dennowiggle/FLEADiP/kicad/FLEADiP.kicad_sch

## KiCad design kicad/FLEADiP.kicad_sch (2023-07-13)

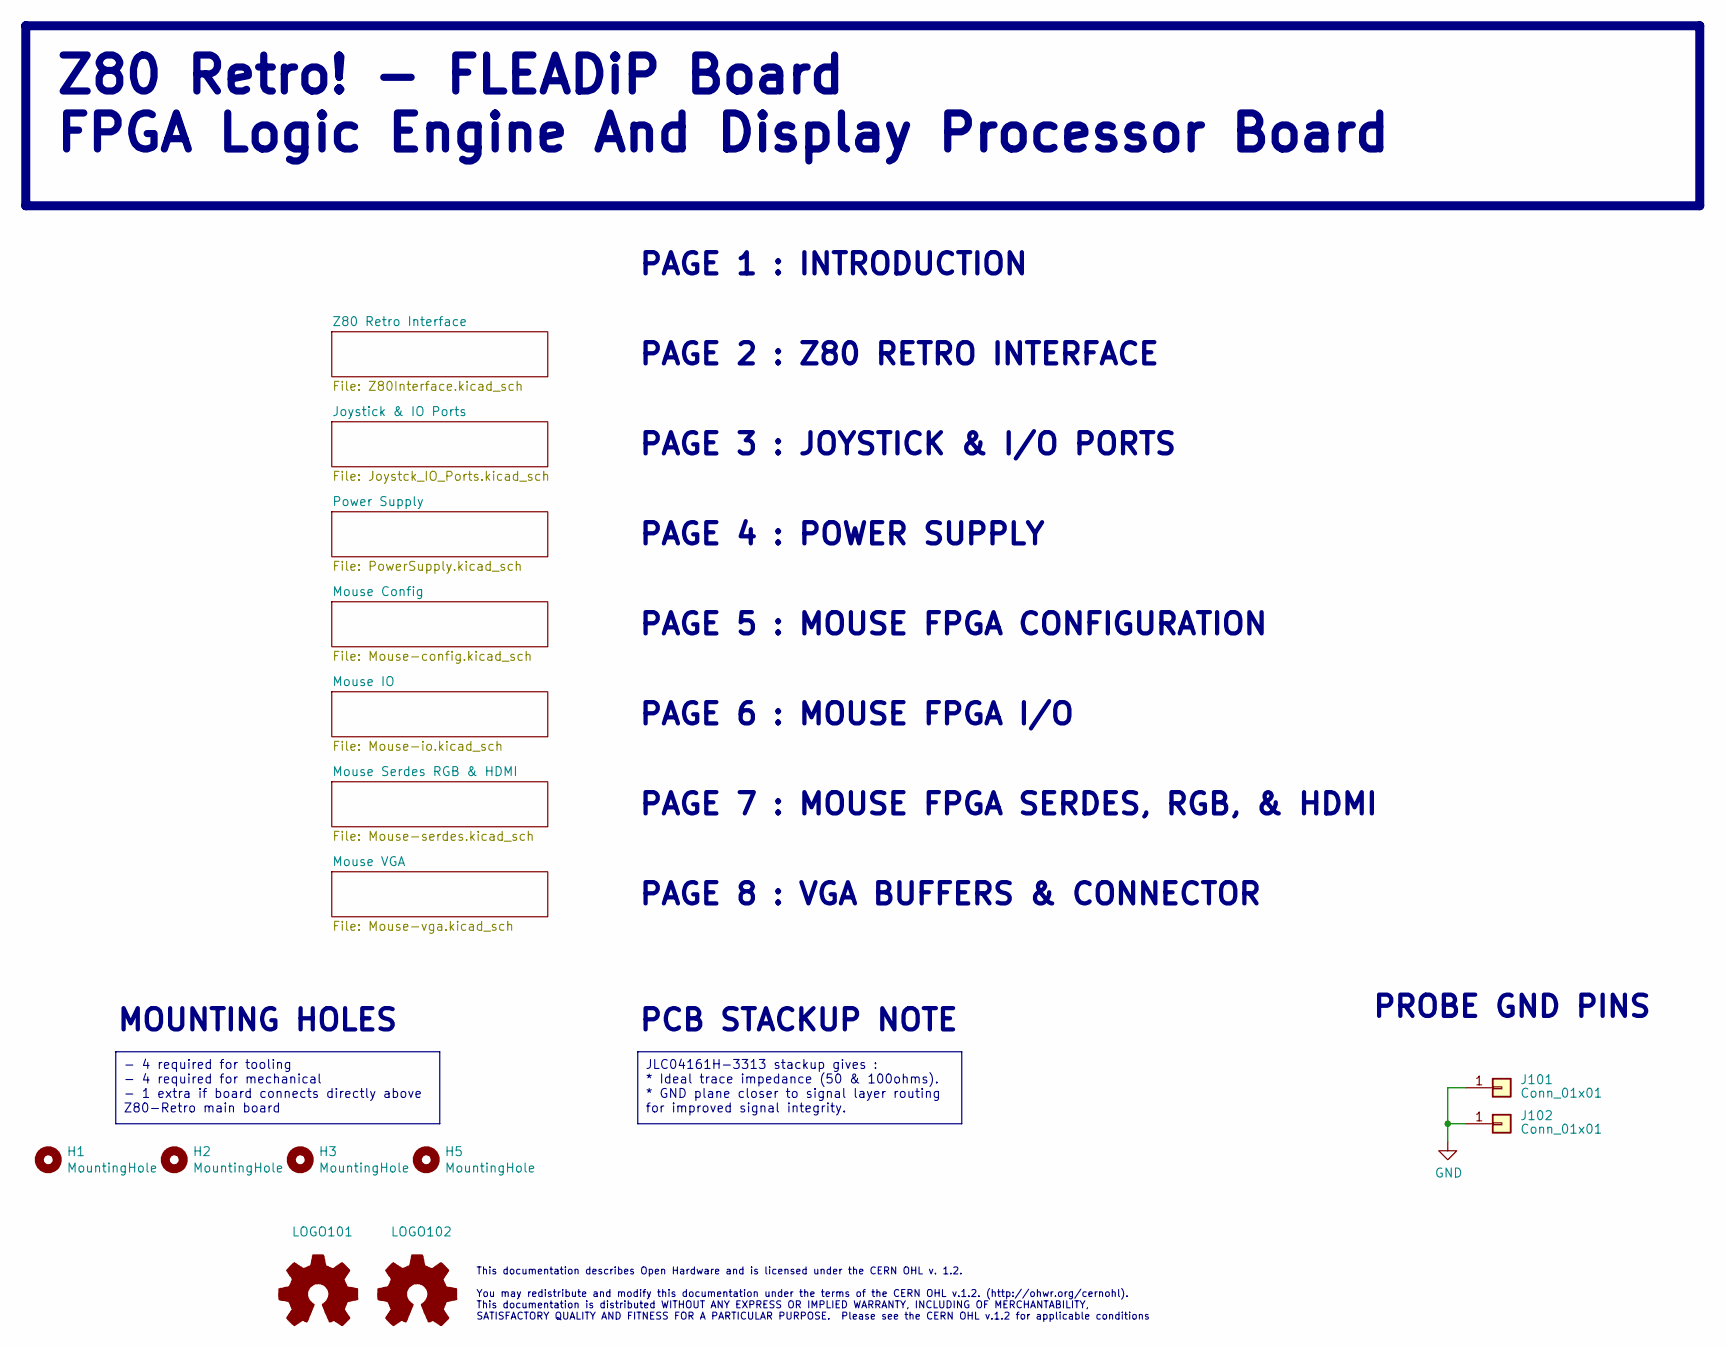
[picture p20: schematic FLEADiP.kicad_sch]

Parts:
H1, H2, H3, H5: MountingHole; MountingHole_2.7mm_M2.5_DIN965
J101, J102: Conn_01x01; PinHeader_1x01_P2.54mm_Vertical
LOGO101, LOGO102: Logo_Open_Hardware_Small; OSHW-Logo_7.5x8mm_SilkScreen

Connections:
GND: J101.1, J102.1

Notes on the sheet:
Z80 Retro! - FLEADiP Board FPGA Logic Engine And Display Processor Board
JLC04161H-3313 stackup gives : * Ideal trace impedance (50 & 100ohms). * GND plane closer to signal layer routing for improved signal integrity.
- 4 required for tooling - 4 required for mechanical - 1 extra if board connects directly above Z80-Retro main board
MOUNTING HOLES
PAGE 5 : MOUSE FPGA CONFIGURATION
PAGE 6 : MOUSE FPGA I/O
PAGE 4 : POWER SUPPLY
PAGE 2 : Z80 RETRO INTERFACE
PCB STACKUP NOTE
PAGE 7 : MOUSE FPGA SERDES, RGB, & HDMI
PROBE GND PINS
PAGE 8 : VGA BUFFERS & CONNECTOR
PAGE 1 : INTRODUCTION
PAGE 3 : JOYSTICK & I/O PORTS
This documentation describes Open Hardware and is licensed under the CERN OHL v. 1.2. You may redistribute and modify this documentation under the terms of the CERN OHL v.1.2. (http://ohwr.org/cernohl). This documentation is distributed WITHOUT ANY EXPRESS OR IMPLIED WARRANTY, INCLUDING OF MERCHANT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
