dennowiggle/FLEADiP/kicad/Joystck_IO_Ports.kicad_sch

## KiCad design kicad/Joystck_IO_Ports.kicad_sch (2023-07-13)

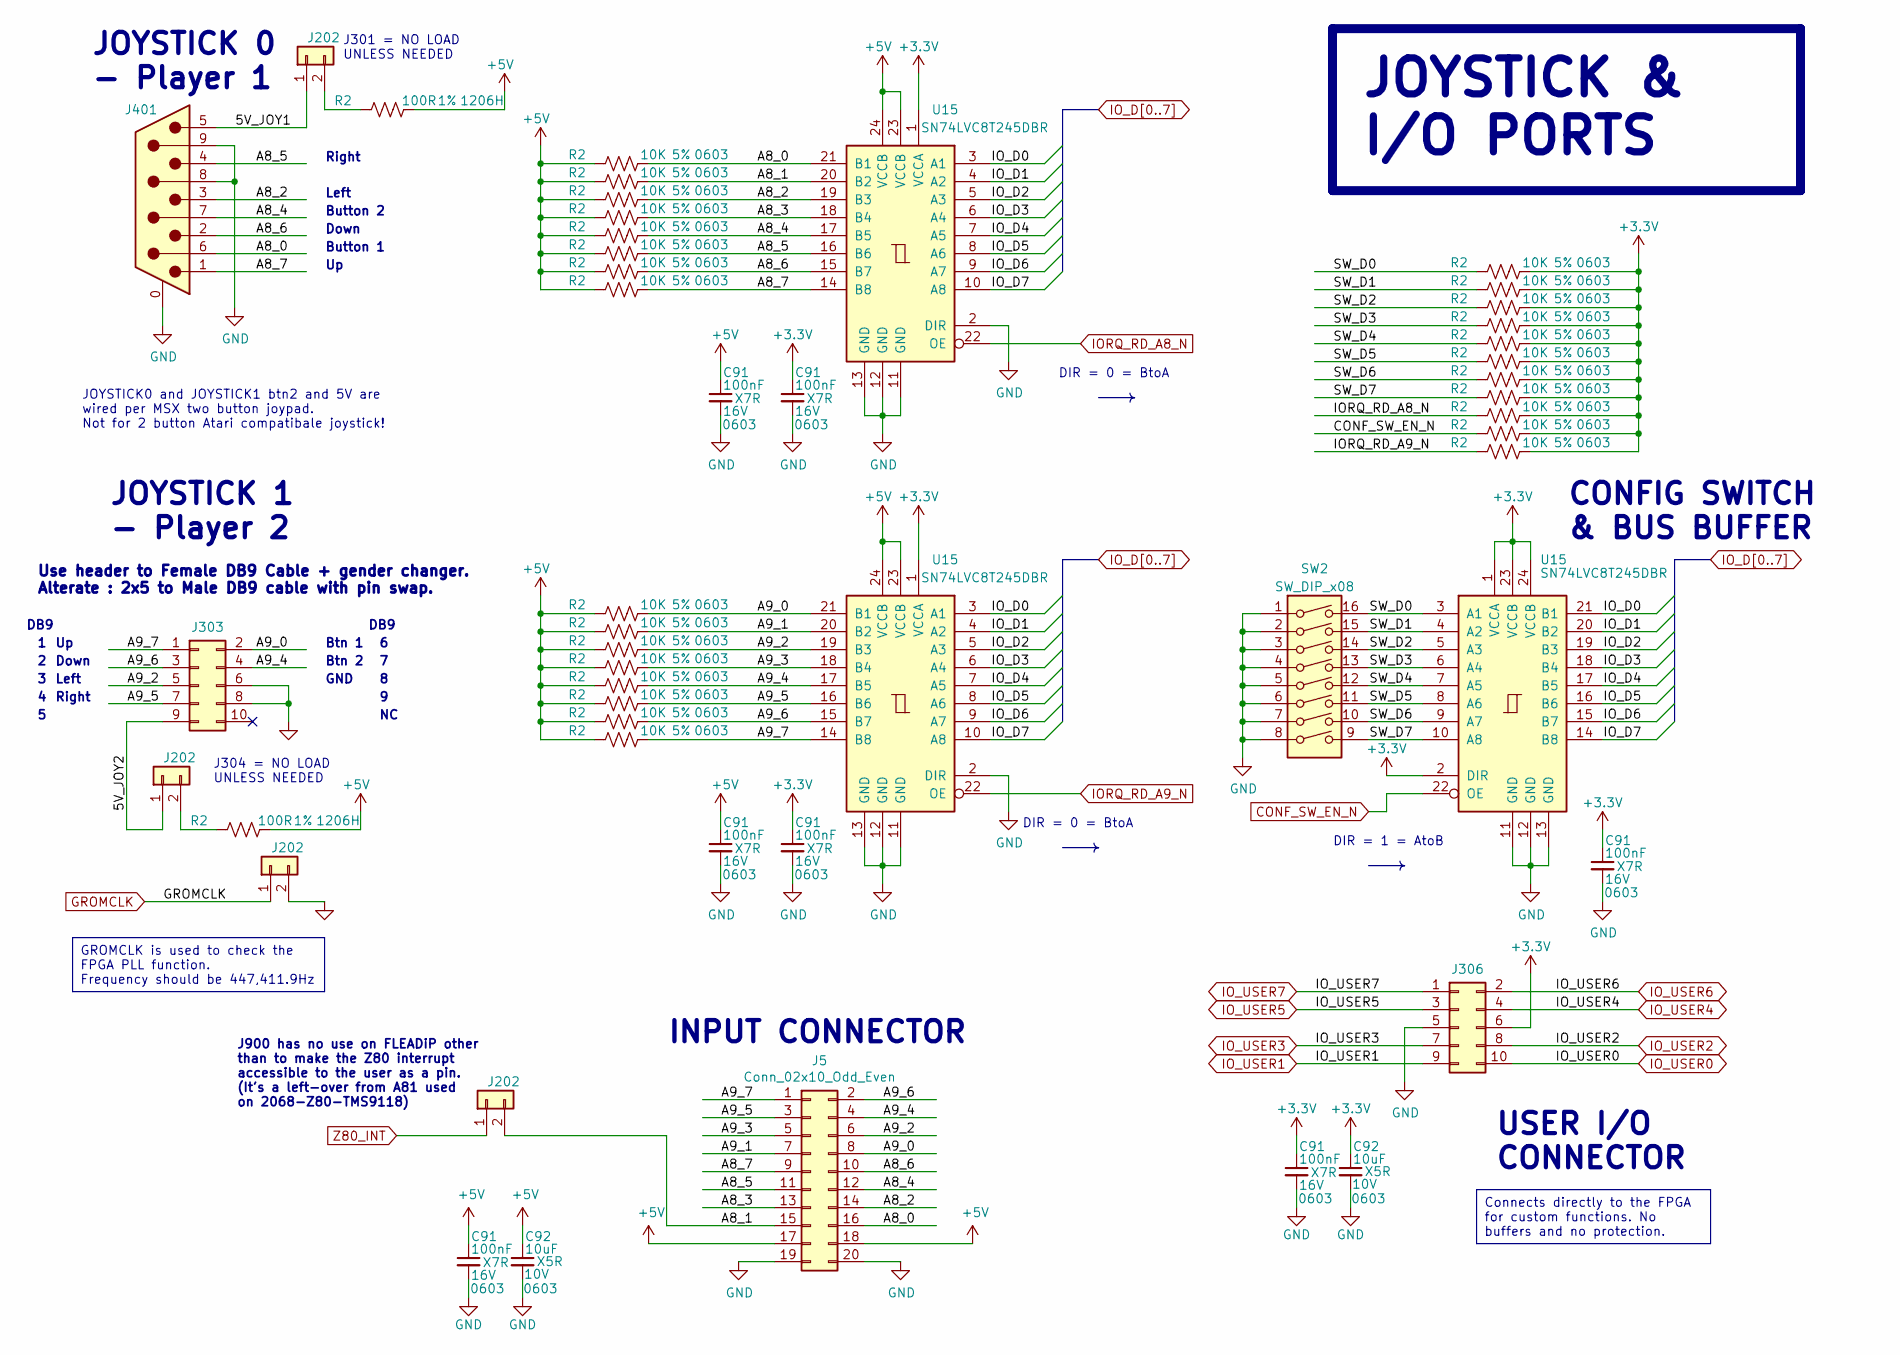
[picture p21: schematic Joystck_IO_Ports.kicad_sch]

Parts:
C91: 100nF; C_0603_1608Metric; Voltage 16V; Tolerance 10%; MPN CC0603KRX7R7BB104; Digikey 311-1088-1-ND
C92: 10uF; C_0603_1608Metric; Voltage 10V; Tolerance 10%; MPN CC0603KRX5R6BB106; Digikey 311-1782-1-ND
J5: Conn_02x10_Odd_Even; PinHeader_2x10_P2.54mm_Vertical; MPN PH2-20-UA; Digi-Key_PN 2057-PH2-20-UA-ND
J202: Conn_01x02; PinHeader_1x02_P2.54mm_Vertical; MPN PH1-02-UA; Digi-Key_PN 2057-PH1-02-UA-ND
J303, J306: Conn_02x05; PinHeader_2x05_P2.54mm_Vertical; MPN PR20205VBDN; Digikey 1849-1002-ND
J401: DB9_Male_MountingHoles; DSUB-9_Male_Horizontal_P2.77x2.84mm_EdgePinOffset7.70mm_Hou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; MPN A-DS 09 A/KG-T4S; Digikey AE10970-ND
R2: 10K; R_0603_1608Metric; Tolerance 5%; MPN RC0603JR-0710KL; Digikey 311-10KGRCT-ND
SW2: SW_DIP_x08; SW_DIP_SPSTx08_Slide_9.78x22.5mm_W7.62mm_P2.54mm; MPN 206-8ST; Digikey CT2068ST-ND
U15: SN74LVC8T245DBR; SSOP-24_5.3x8.2mm_P0.65mm; MPN SN74LVC8T245DBR; Digikey 296-21065-1-ND

Connections:
5V_JOY1: J202.1, J401.5
5V_JOY2: J202.1, J303.9
+3.3V: C91.1, C92.1, J306.6, R2.2, U15.1 (VCCA), U15.2 (DIR), U15.23 (VCCB), U15.24 (VCCB)
+5V: C91.1, C92.1, J5.17, J5.18, R2.1, R2.2, U15.23 (VCCB), U15.24 (VCCB)
A8_0: J5.16, J401.6, R2.2, U15.21 (B1)
A8_1: J5.15, J202.2, R2.2, U15.20 (B2)
A8_2: J5.14, J401.3, R2.2, U15.19 (B3)
A8_3: J5.13, R2.2, U15.18 (B4)
A8_4: J5.12, J401.7, R2.2, U15.17 (B5)
A8_5: J5.11, J401.4, R2.2, U15.16 (B6)
A8_6: J5.10, J401.2, R2.2, U15.15 (B7)
A8_7: J5.9, J401.1, R2.2, U15.14 (B8)
A9_0: J5.8, J303.2, R2.2, U15.21 (B1)
A9_1: J5.7, R2.2, U15.20 (B2)
A9_2: J5.6, J303.5, R2.2, U15.19 (B3)
A9_3: J5.5, R2.2, U15.18 (B4)
A9_4: J5.4, J303.4, R2.2, U15.17 (B5)
A9_5: J5.3, J303.7, R2.2, U15.16 (B6)
A9_6: J5.2, J303.3, R2.2, U15.15 (B7)
A9_7: J5.1, J303.1, R2.2, U15.14 (B8)
CONF_SW_EN_N: R2.1, U15.22 (OE)
GND: C91.2, C92.2, J5.19, J5.20, J202.2, J303.6, J303.8, J306.5, J401.0 (PAD), J401.8, J401.9, SW2.1, SW2.2, SW2.3, SW2.4, SW2.5, SW2.6, SW2.7, SW2.8, U15.2 (DIR), U15.11 (GND), U15.12 (GND), U15.13 (GND)
GROMCLK: J202.1
IORQ_RD_A8_N: R2.1, U15.22 (OE)
IORQ_RD_A9_N: R2.1, U15.22 (OE)
IO_D0: U15.3 (A1), U15.21 (B1)
IO_D1: U15.4 (A2), U15.20 (B2)
IO_D2: U15.5 (A3), U15.19 (B3)
IO_D3: U15.6 (A4), U15.18 (B4)
IO_D4: U15.7 (A5), U15.17 (B5)
IO_D5: U15.8 (A6), U15.16 (B6)
IO_D6: U15.9 (A7), U15.15 (B7)
IO_D7: U15.10 (A8), U15.14 (B8)
IO_USER0: J306.10
IO_USER1: J306.9
IO_USER2: J306.8
IO_USER3: J306.7
IO_USER4: J306.4
IO_USER5: J306.3
IO_USER6: J306.2
IO_USER7: J306.1
unnamed: J202.2, R2.1
SW_D0: R2.1, SW2.16, U15.3 (A1)
SW_D1: R2.1, SW2.15, U15.4 (A2)
SW_D2: R2.1, SW2.14, U15.5 (A3)
SW_D3: R2.1, SW2.13, U15.6 (A4)
SW_D4: R2.1, SW2.12, U15.7 (A5)
SW_D5: R2.1, SW2.11, U15.8 (A6)
SW_D6: R2.1, SW2.10, U15.9 (A7)
SW_D7: R2.1, SW2.9, U15.10 (A8)
Z80_INT: J202.1

Notes on the sheet:
GROMCLK is used to check the FPGA PLL function. Frequency should be 447,411.9Hz
Connects directly to the FPGA for custom functions. No buffers and no protection.
JOYSTICK & I/O PORTS
Button 1
GND
DB9
J900 has no use on FLEADiP other than to make the Z80 interrupt accessible to the user as a pin. (It's a left-over from A81 used on 2068-Z80-TMS9118)
Left
Down
J301 = NO LOAD UNLESS NEEDED
INPUT CONNECTOR
J304 = NO LOAD UNLESS NEEDED
DIR = 0 = BtoA
USER I/O CONNECTOR
CONFIG SWITCH & BUS BUFFER
Use header to Female DB9 Cable + gender changer. Alterate : 2x5 to Male DB9 cable with pin swap.
Right
Btn 2
Btn 1
JOYSTICK 1 - Player 2
JOYSTICK0 and JOYSTICK1 btn2 and 5V are wired per MSX two button joypad. Not for 2 button Atari compatibale joystick!
Button 2
JOYSTICK 0 - Player 1
DIR = 1 = AtoB
