dennowiggle/FLEADiP/kicad/Mouse-config.kicad_sch

## KiCad design kicad/Mouse-config.kicad_sch (2023-07-13)

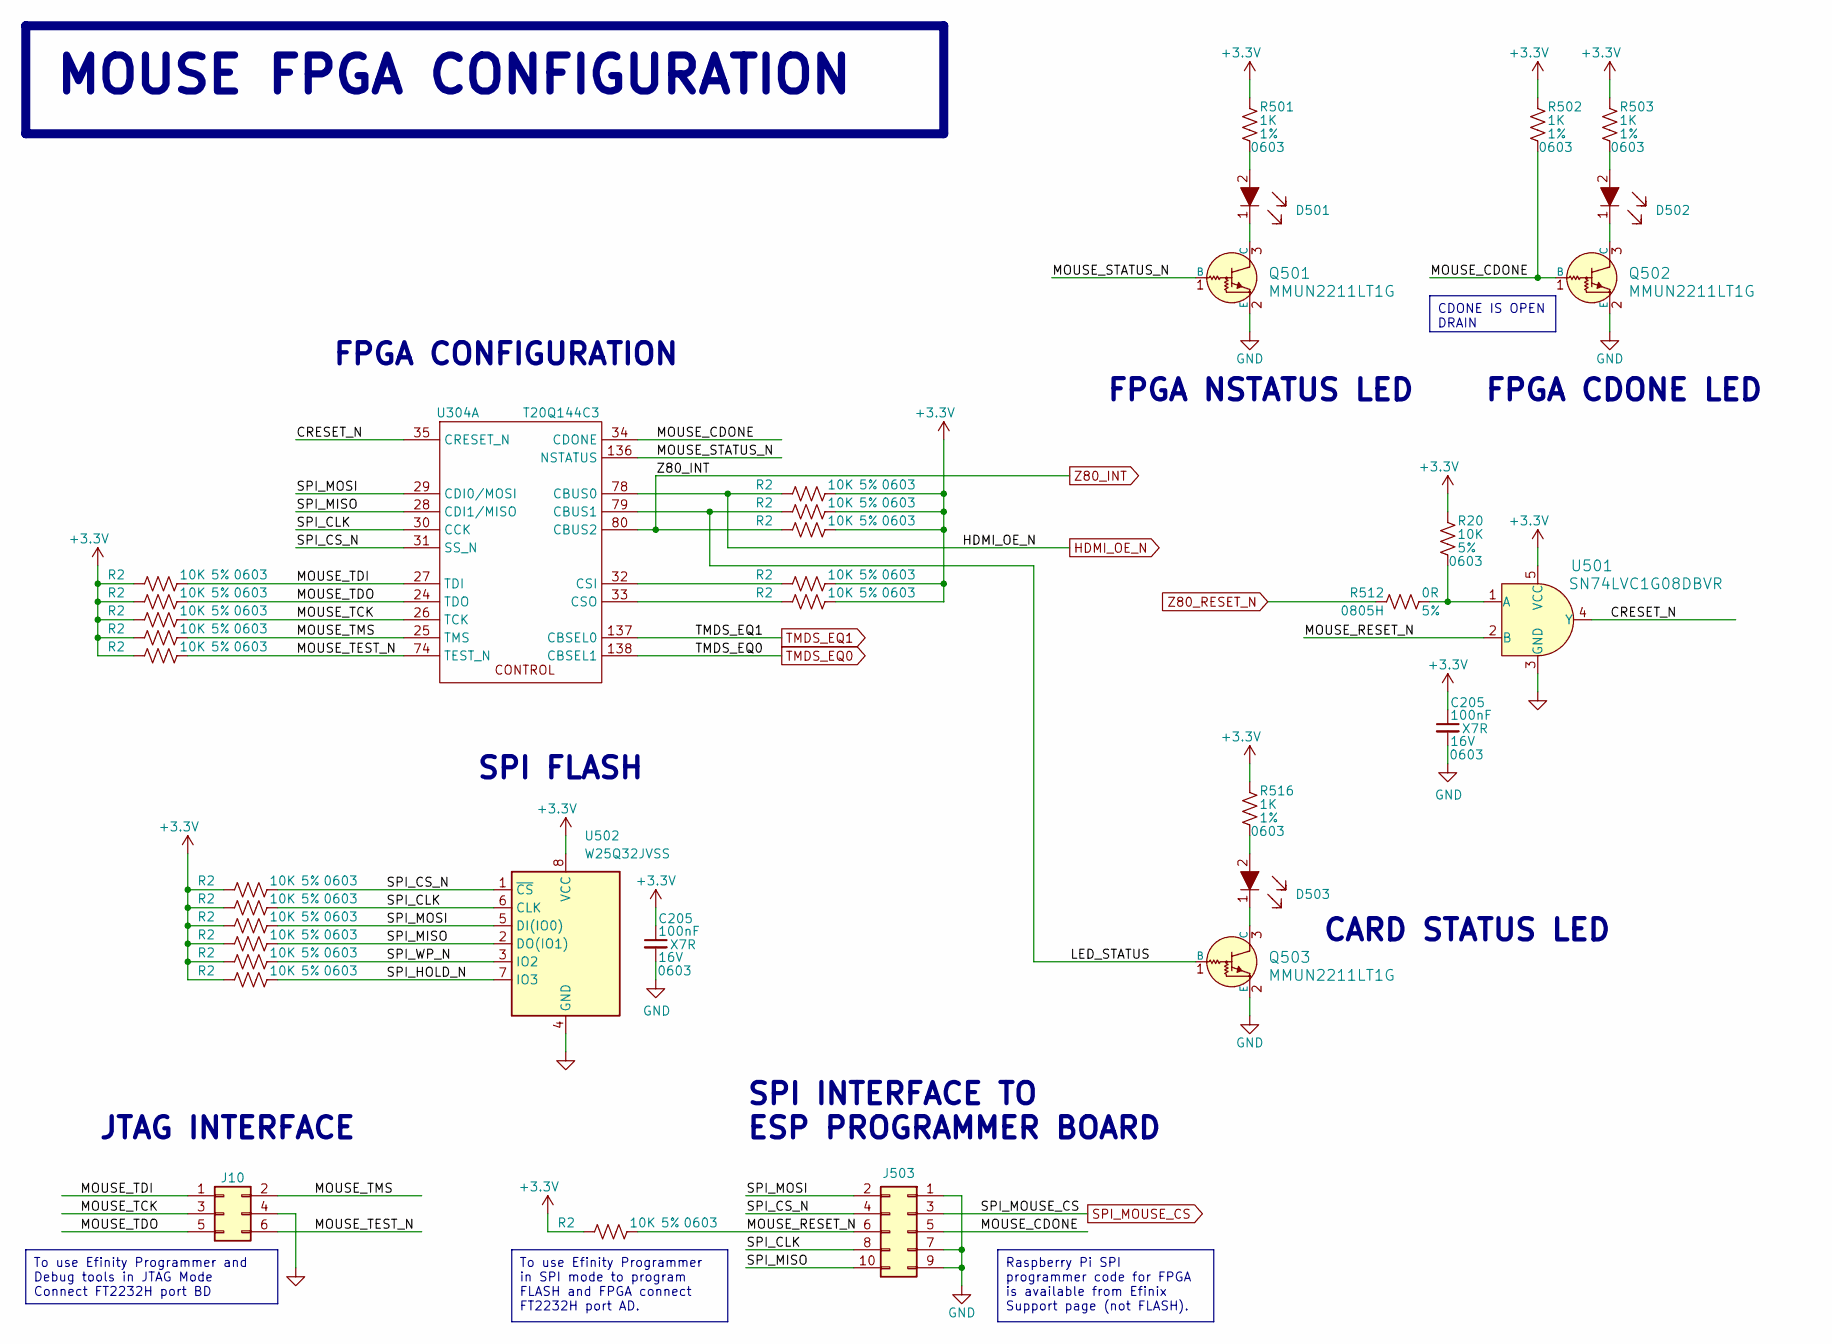
[picture p22: schematic Mouse-config.kicad_sch]

Parts:
C205: 100nF; C_0603_1608Metric; Voltage 16V; Tolerance 10%; MPN CC0603KRX7R7BB104; Digikey 311-1088-1-ND
D501, D502, D503: LTST-C191KRKT; LED_0603_1608Metric; MPN LTST-C191GKT; Digikey 160-1443-1-ND
J10: Conn_02x03; PinHeader_2x03_P2.54mm_Vertical; MPN PH2-06-UA; Digikey 2057-PH2-06-UA-ND
J503: Conn_02x05_Right_Angle; PinSocket_2x05_P2.54mm_Vertical; MPN PH2RA-10-UA; Digikey 2057-PH2RA-10-UA-ND
Q501, Q502, Q503: MMUN2211LT1G; SOT-23-3; MPN MMUN2211LT1G; Digikey MMUN2211LT1GOSCT-ND
R2, R20: 10K; R_0603_1608Metric; Tolerance 5%; MPN RC0603JR-0710KL; Digikey 311-10KGRCT-ND
R501, R502, R503, R516: 1K; R_0603_1608Metric; Tolerance 1%; MPN RC0603FR-071KL; Digikey 311-1.00KHRCT-ND
R512: 0R; R_0805_2012Metric_Pad1.20x1.40mm_HandSolder; Tolerance 5%; MPN RC0805JR-070RL; Digikey 311-0.0ARCT-ND
U304: T20Q144C3; LQFP-144_20x20mm_P0.5mm; MPN T20Q144C3; Digikey 2134-T20Q144C3-ND
U501: SN74LVC1G08DBVR; SOT-23-5; MPN SN74LVC1G08DBVR; Digikey 296-11601-1-ND
U502: W25Q32JVSS; SOIC-8_5.23x5.23mm_P1.27mm; MPN W25Q32JVSSIQ; Digikey W25Q32JVSSIQCT-ND

Connections:
+3.3V: C205.1, R2.1, R2.2, R20.1, R501.1, R502.1, R503.1, R516.1, U501.5 (VCC), U502.8 (VCC)
CRESET_N: U304.35 (CRESET_N), U501.4 (Y)
GND: C205.2, J10.4, J503.1, J503.7, J503.9, Q501.2 (E), Q502.2 (E), Q503.2 (E), U501.3 (GND), U502.4 (GND)
HDMI_OE_N: R2.1, U304.78 (CBUS0)
LED_STATUS: Q503.1 (B), R2.1, U304.79 (CBUS1)
MOUSE_CDONE: J503.5, Q502.1 (B), R502.2, U304.34 (CDONE)
MOUSE_RESET_N: J503.6, R2.2, U501.2 (B)
MOUSE_STATUS_N: Q501.1 (B), U304.136 (NSTATUS)
MOUSE_TCK: J10.3, R2.2, U304.26 (TCK)
MOUSE_TDI: J10.1, R2.2, U304.27 (TDI)
MOUSE_TDO: J10.5, R2.2, U304.24 (TDO)
MOUSE_TEST_N: J10.6, R2.2, U304.74 (TEST_N)
MOUSE_TMS: J10.2, R2.2, U304.25 (TMS)
unnamed: D501.1, Q501.3 (C)
unnamed: D501.2, R501.2
unnamed: D502.1, Q502.3 (C)
unnamed: D502.2, R503.2
unnamed: D503.1, Q503.3 (C)
unnamed: D503.2, R516.2
unnamed: R2.1, U304.32 (CSI), U304.33 (CSO)
unnamed: R20.2, R512.2, U501.1 (A)
SPI_CLK: J503.8, R2.2, U304.30 (CCK), U502.6 (CLK)
SPI_CS_N: J503.4, R2.2, U304.31 (SS_N), U502.1 (~CS)
SPI_HOLD_N: R2.2, U502.7 (IO3)
SPI_MISO: J503.10, R2.2, U304.28 (CDI1/MISO), U502.2 (DO(IO1))
SPI_MOSI: J503.2, R2.2, U304.29 (CDI0/MOSI), U502.5 (DI(IO0))
SPI_MOUSE_CS: J503.3
SPI_WP_N: R2.2, U502.3 (IO2)
TMDS_EQ0: U304.138 (CBSEL1)
TMDS_EQ1: U304.137 (CBSEL0)
Z80_INT: R2.1, U304.80 (CBUS2)
Z80_RESET_N: R512.1

Notes on the sheet:
CDONE IS OPEN DRAIN
To use Efinity Programmer in SPI mode to program FLASH and FPGA connect FT2232H port AD.
Raspberry Pi SPI programmer code for FPGA is available from Efinix Support page (not FLASH).
MOUSE FPGA CONFIGURATION
To use Efinity Programmer and Debug tools in JTAG Mode Connect FT2232H port BD
SPI FLASH
JTAG INTERFACE
CARD STATUS LED
SPI INTERFACE TO ESP PROGRAMMER BOARD
FPGA NSTATUS LED
FPGA CONFIGURATION
FPGA CDONE LED
