dennowiggle/FLEADiP/kicad/Mouse-io.kicad_sch

## KiCad design kicad/Mouse-io.kicad_sch (2023-07-13)

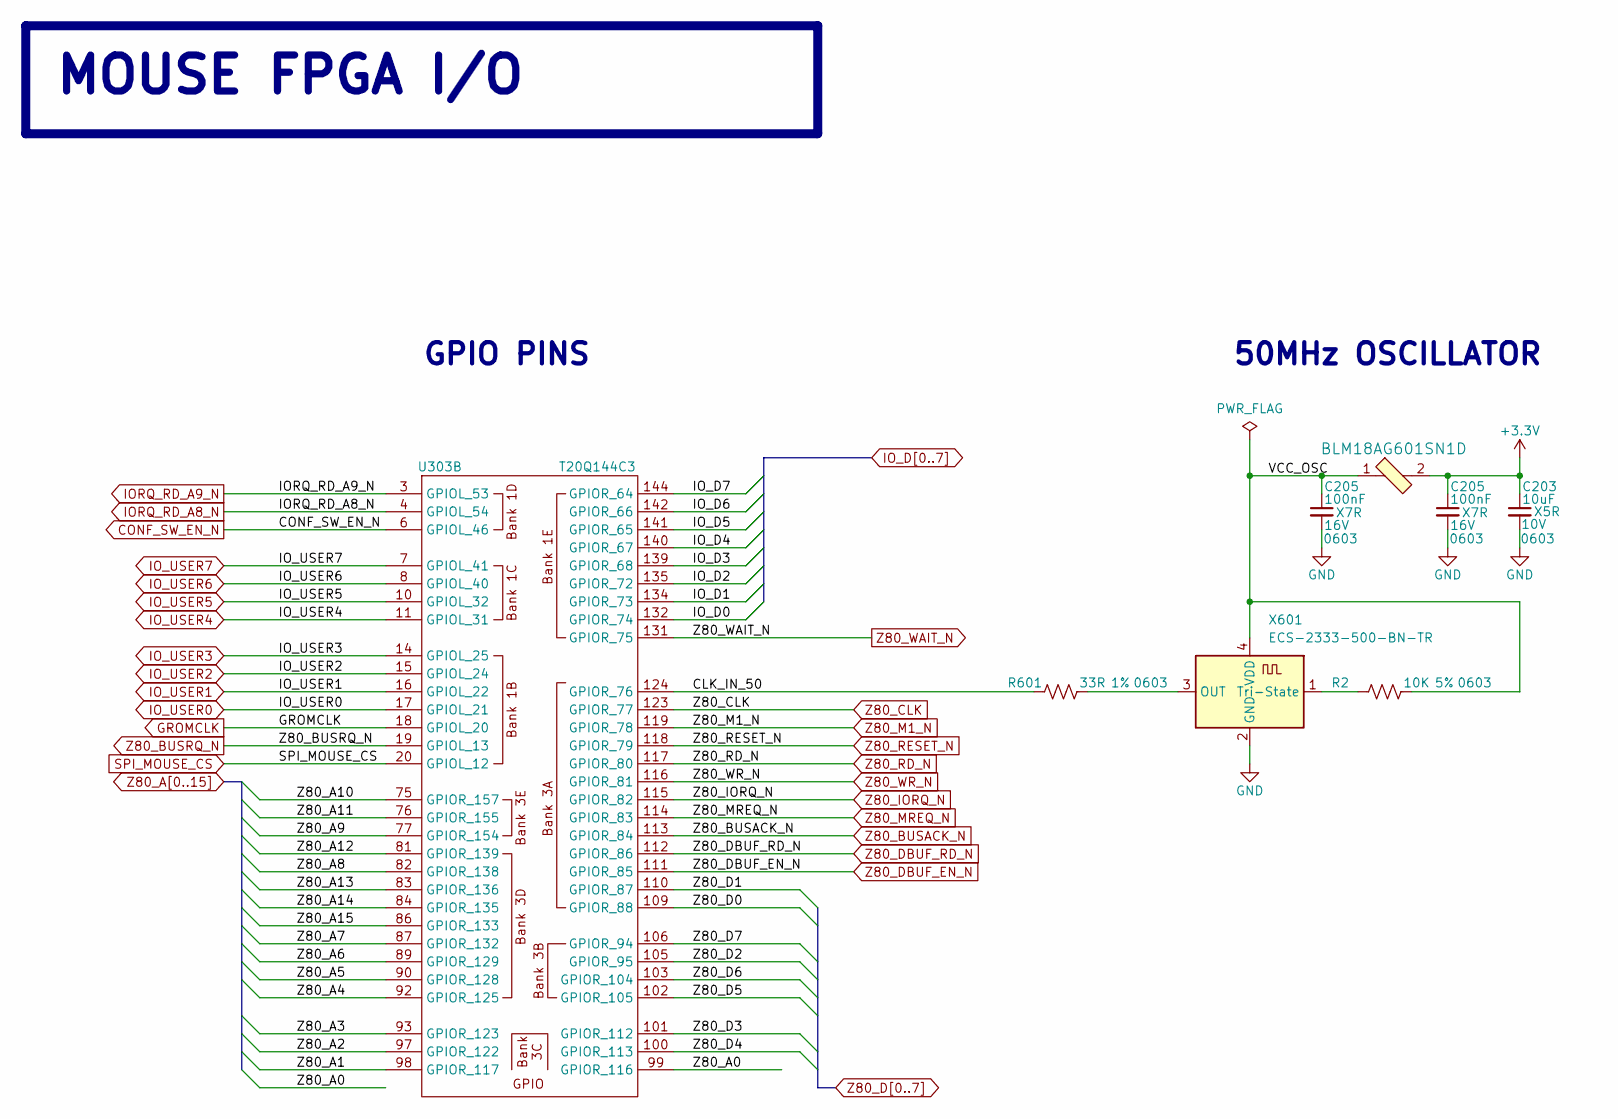
[picture p23: schematic Mouse-io.kicad_sch]

Parts:
C203: 10uF; C_0603_1608Metric; Voltage 10V; Tolerance 10%; MPN CC0603KRX5R6BB106; Digikey 311-1782-1-ND
C205: 100nF; C_0603_1608Metric; Voltage 16V; Tolerance 10%; MPN CC0603KRX7R7BB104; Digikey 311-1088-1-ND
FB2: BLM18AG601SN1D; L_0603_1608Metric; MPN BLM18AG601SN1D; Digikey 490-1014-1-ND
R2: 10K; R_0603_1608Metric; Tolerance 5%; MPN RC0603JR-0710KL; Digikey 311-10KGRCT-ND
R601: 33R; R_0603_1608Metric; Tolerance 1%; MPN RC0603FR-0733RL; Digikey 13-RC0603FR-0733RLCT-ND
U303: T20Q144C3; LQFP-144_20x20mm_P0.5mm; MPN T20Q144C3; Digikey 2134-T20Q144C3-ND
X601: ECS-2333-500-BN-TR; Oscillator_SMD_EuroQuartz_XO32-4Pin_3.2x2.5mm; MPN ECS-2333-500-BN-TR; Digikey XC1930CT-ND

Connections:
+3.3V: C203.1, C205.1, FB2.2
CLK_IN_50: R601.1, U303.124 (GPIOR_76)
CONF_SW_EN_N: U303.6 (GPIOL_46)
GND: C203.2, C205.2, X601.2 (GND)
GROMCLK: U303.18 (GPIOL_20)
IORQ_RD_A8_N: U303.4 (GPIOL_54)
IORQ_RD_A9_N: U303.3 (GPIOL_53)
IO_D0: U303.132 (GPIOR_74)
IO_D1: U303.134 (GPIOR_73)
IO_D2: U303.135 (GPIOR_72)
IO_D3: U303.139 (GPIOR_68)
IO_D4: U303.140 (GPIOR_67)
IO_D5: U303.141 (GPIOR_65)
IO_D6: U303.142 (GPIOR_66)
IO_D7: U303.144 (GPIOR_64)
IO_USER0: U303.17 (GPIOL_21)
IO_USER1: U303.16 (GPIOL_22)
IO_USER2: U303.15 (GPIOL_24)
IO_USER3: U303.14 (GPIOL_25)
IO_USER4: U303.11 (GPIOL_31)
IO_USER5: U303.10 (GPIOL_32)
IO_USER6: U303.8 (GPIOL_40)
IO_USER7: U303.7 (GPIOL_41)
unnamed: R2.1, X601.1 (Tri-State)
unnamed: R601.2, X601.3 (OUT)
SPI_MOUSE_CS: U303.20 (GPIOL_12)
VCC_OSC: C205.1, FB2.1, R2.2, X601.4 (VDD)
Z80_A0: U303.99 (GPIOR_116)
Z80_A1: U303.98 (GPIOR_117)
Z80_A2: U303.97 (GPIOR_122)
Z80_A3: U303.93 (GPIOR_123)
Z80_A4: U303.92 (GPIOR_125)
Z80_A5: U303.90 (GPIOR_128)
Z80_A6: U303.89 (GPIOR_129)
Z80_A7: U303.87 (GPIOR_132)
Z80_A8: U303.82 (GPIOR_138)
Z80_A9: U303.77 (GPIOR_154)
Z80_A10: U303.75 (GPIOR_157)
Z80_A11: U303.76 (GPIOR_155)
Z80_A12: U303.81 (GPIOR_139)
Z80_A13: U303.83 (GPIOR_136)
Z80_A14: U303.84 (GPIOR_135)
Z80_A15: U303.86 (GPIOR_133)
Z80_BUSACK_N: U303.113 (GPIOR_84)
Z80_BUSRQ_N: U303.19 (GPIOL_13)
Z80_CLK: U303.123 (GPIOR_77)
Z80_D0: U303.109 (GPIOR_88)
Z80_D1: U303.110 (GPIOR_87)
Z80_D2: U303.105 (GPIOR_95)
Z80_D3: U303.101 (GPIOR_112)
Z80_D4: U303.100 (GPIOR_113)
Z80_D5: U303.102 (GPIOR_105)
Z80_D6: U303.103 (GPIOR_104)
Z80_D7: U303.106 (GPIOR_94)
Z80_DBUF_EN_N: U303.111 (GPIOR_85)
Z80_DBUF_RD_N: U303.112 (GPIOR_86)
Z80_IORQ_N: U303.115 (GPIOR_82)
Z80_M1_N: U303.119 (GPIOR_78)
Z80_MREQ_N: U303.114 (GPIOR_83)
Z80_RD_N: U303.117 (GPIOR_80)
Z80_RESET_N: U303.118 (GPIOR_79)
Z80_WAIT_N: U303.131 (GPIOR_75)
Z80_WR_N: U303.116 (GPIOR_81)

Notes on the sheet:
MOUSE FPGA I/O
50MHz OSCILLATOR
GPIO PINS
