dennowiggle/FLEADiP/kicad/Mouse-serdes.kicad_sch

## KiCad design kicad/Mouse-serdes.kicad_sch (2023-07-13)

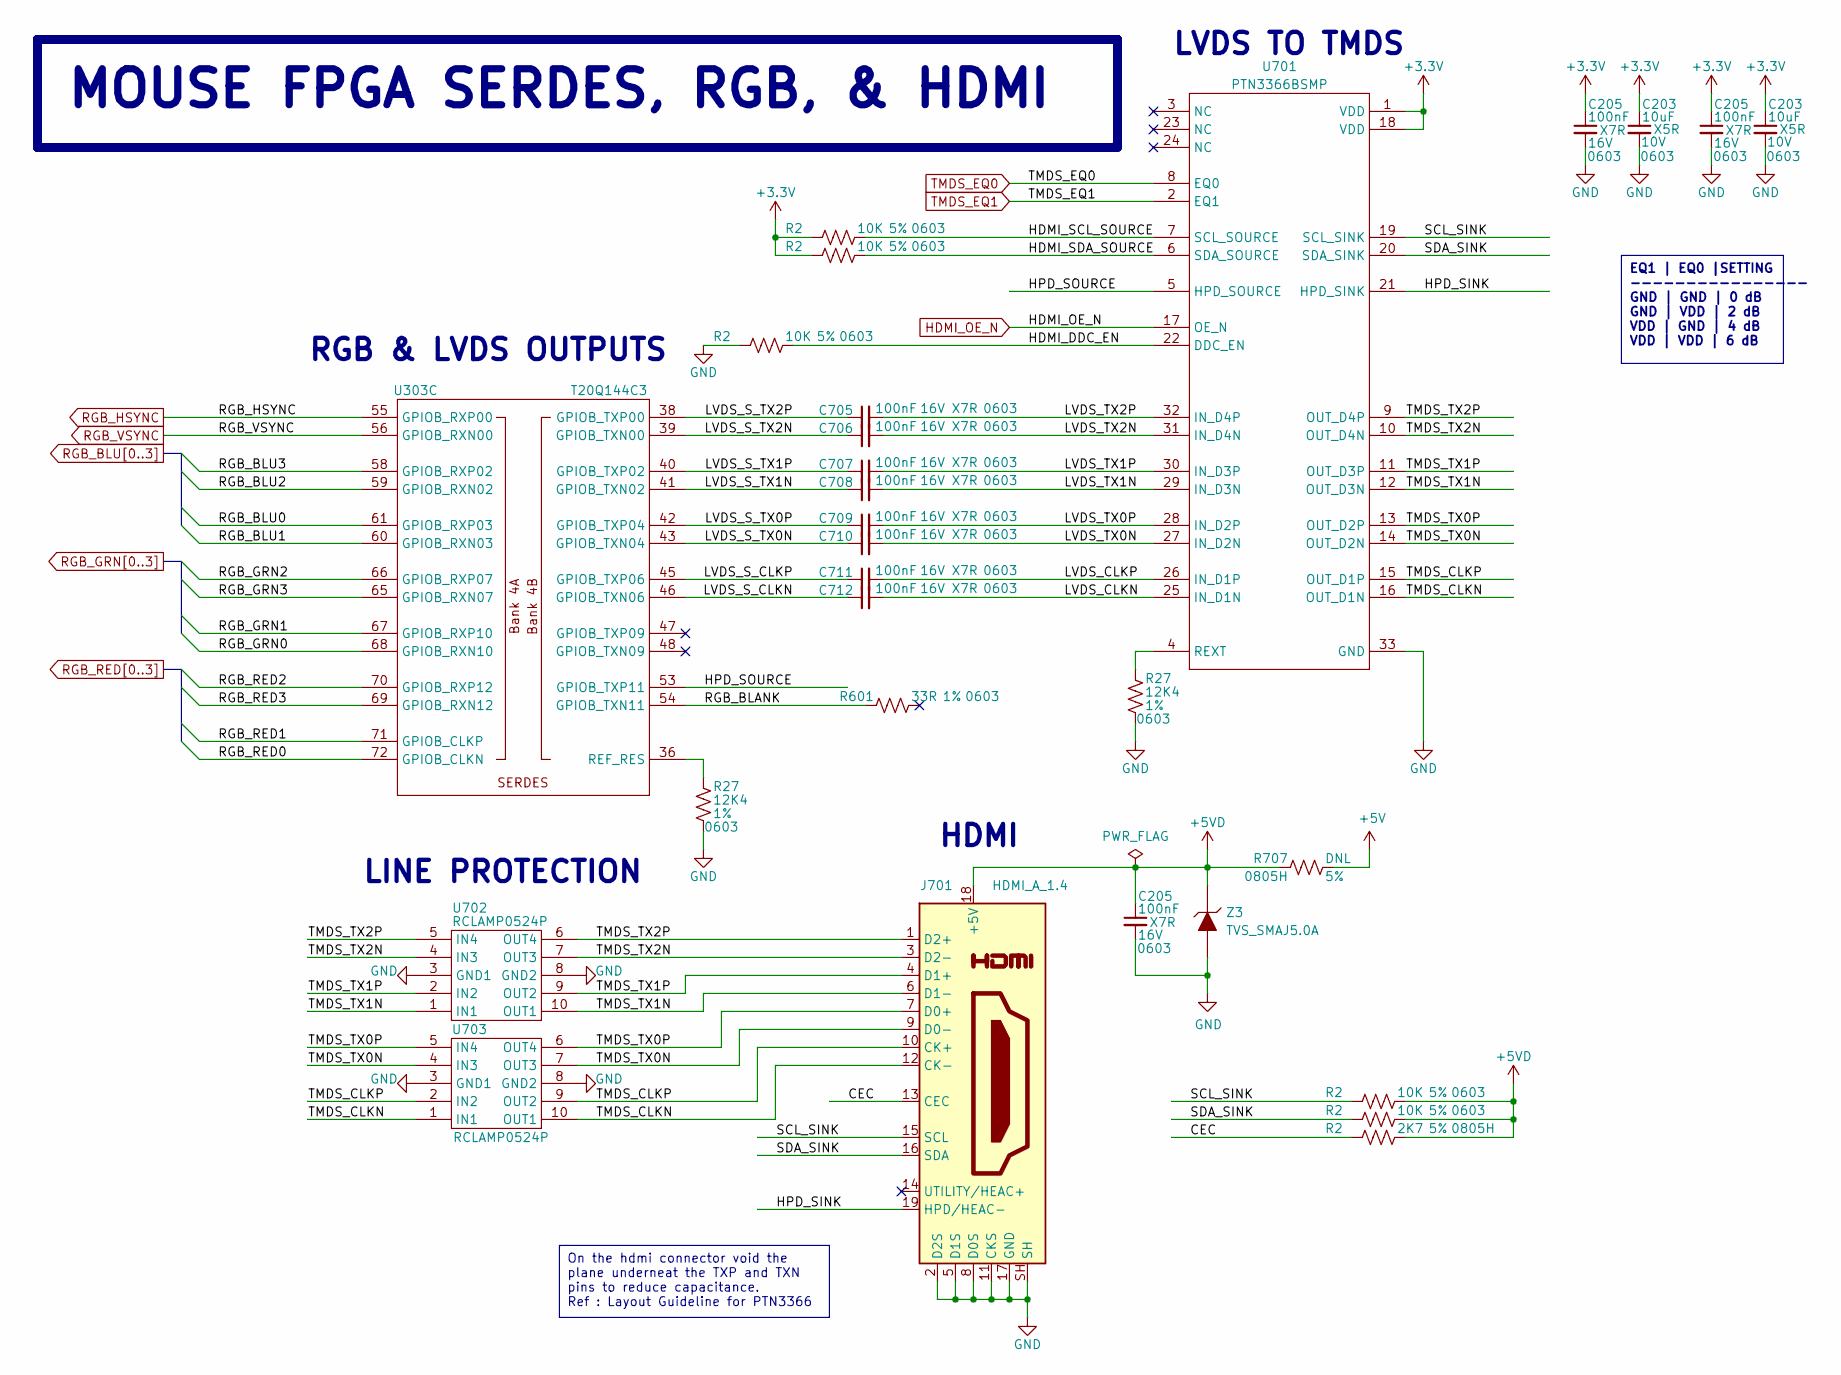
[picture p24: schematic Mouse-serdes.kicad_sch]

Parts:
C203: 10uF; C_0603_1608Metric; Voltage 10V; Tolerance 10%; MPN CC0603KRX5R6BB106; Digikey 311-1782-1-ND
C205, C705, C706, C707, C708, C709, C710, C711, C712: 100nF; C_0603_1608Metric; Voltage 16V; Tolerance 10%; MPN CC0603KRX7R7BB104; Digikey 311-1088-1-ND
J701: HDMI_A_1.4; HDMI_A_Amphenol_10029449-x01xLF_Horizontal; MPN 10029449-111RLF; Digikey 609-4614-1-ND
R2: 10K; R_0603_1608Metric; Tolerance 5%; MPN RC0603JR-0710KL; Digikey 311-10KGRCT-ND
R27: 12K4; R_0603_1608Metric; Tolerance 1%; MPN RC0603FR-0712K4L; Digikey 311-12.4KHRCT-ND
R601: 33R; R_0603_1608Metric; Tolerance 1%; MPN RC0603FR-0733RL; Digikey 13-RC0603FR-0733RLCT-ND
R707: DNL; R_0805_2012Metric_Pad1.20x1.40mm_HandSolder; Tolerance 5%; MPN RC0805JR-070RL; Digikey 311-0.0ARCT-ND
U303: T20Q144C3; LQFP-144_20x20mm_P0.5mm; MPN T20Q144C3; Digikey 2134-T20Q144C3-ND
U701: PTN3366BSMP; HVQFN-32-1EP_5x5mm_P0.5mm_EP3.1x3.1mm_ThermalVias; MPN PTN3366BSMP; Digikey 568-13387-1-ND
U702, U703: RCLAMP0524P; UFDFN-10_2.5x1mm; MPN RCLAMP0524P.TCT; Digikey RCLAMP0524PCT-ND
Z3: TVS_SMAJ5.0A; D_SMA_Handsoldering; MPN SMAJ5.0; Digikey SMAJ5.0ALFCT-ND

Connections:
+3.3V: C203.1, C205.1, R2.1, U701.1 (VDD), U701.18 (VDD)
+5V: R707.2
+5VD: C205.1, J701.18 (+5V), R2.2, R707.1, Z3.1
CEC: J701.13 (CEC), R2.1
GND: C203.2, C205.2, J701.2 (D2S), J701.5 (D1S), J701.8 (D0S), J701.11 (CKS), J701.17 (GND), J701.SH, R2.1, R27.2, U701.33 (GND), U702.3 (GND1), U702.8 (GND2), U703.3 (GND1), U703.8 (GND2), Z3.2
HDMI_DDC_EN: R2.2, U701.22 (DDC_EN)
HDMI_OE_N: U701.17 (OE_N)
HDMI_SCL_SOURCE: R2.2, U701.7 (SCL_SOURCE)
HDMI_SDA_SOURCE: R2.2, U701.6 (SDA_SOURCE)
HPD_SINK: J701.19 (HPD/HEAC-), U701.21 (HPD_SINK)
HPD_SOURCE: U303.53 (GPIOB_TXP11), U701.5 (HPD_SOURCE)
LVDS_CLKN: C712.2, U701.25 (IN_D1N)
LVDS_CLKP: C711.2, U701.26 (IN_D1P)
LVDS_S_CLKN: C712.1, U303.46 (GPIOB_TXN06)
LVDS_S_CLKP: C711.1, U303.45 (GPIOB_TXP06)
LVDS_S_TX0N: C710.1, U303.43 (GPIOB_TXN04)
LVDS_S_TX0P: C709.1, U303.42 (GPIOB_TXP04)
LVDS_S_TX1N: C708.1, U303.41 (GPIOB_TXN02)
LVDS_S_TX1P: C707.1, U303.40 (GPIOB_TXP02)
LVDS_S_TX2N: C706.1, U303.39 (GPIOB_TXN00)
LVDS_S_TX2P: C705.1, U303.38 (GPIOB_TXP00)
LVDS_TX0N: C710.2, U701.27 (IN_D2N)
LVDS_TX0P: C709.2, U701.28 (IN_D2P)
LVDS_TX1N: C708.2, U701.29 (IN_D3N)
LVDS_TX1P: C707.2, U701.30 (IN_D3P)
LVDS_TX2N: C706.2, U701.31 (IN_D4N)
LVDS_TX2P: C705.2, U701.32 (IN_D4P)
unnamed: R27.1, U303.36 (REF_RES), U701.4 (REXT)
RGB_BLANK: R601.1, U303.54 (GPIOB_TXN11)
RGB_BLU0: U303.61 (GPIOB_RXP03)
RGB_BLU1: U303.60 (GPIOB_RXN03)
RGB_BLU2: U303.59 (GPIOB_RXN02)
RGB_BLU3: U303.58 (GPIOB_RXP02)
RGB_GRN0: U303.68 (GPIOB_RXN10)
RGB_GRN1: U303.67 (GPIOB_RXP10)
RGB_GRN2: U303.66 (GPIOB_RXP07)
RGB_GRN3: U303.65 (GPIOB_RXN07)
RGB_HSYNC: U303.55 (GPIOB_RXP00)
RGB_RED0: U303.72 (GPIOB_CLKN)
RGB_RED1: U303.71 (GPIOB_CLKP)
RGB_RED2: U303.70 (GPIOB_RXP12)
RGB_RED3: U303.69 (GPIOB_RXN12)
RGB_VSYNC: U303.56 (GPIOB_RXN00)
SCL_SINK: J701.15 (SCL), R2.1, U701.19 (SCL_SINK)
SDA_SINK: J701.16 (SDA), R2.1, U701.20 (SDA_SINK)
TMDS_CLKN: J701.12 (CK-), U701.16 (OUT_D1N), U703.1 (IN1), U703.10 (OUT1)
TMDS_CLKP: J701.10 (CK+), U701.15 (OUT_D1P), U703.2 (IN2), U703.9 (OUT2)
TMDS_EQ0: U701.8 (EQ0)
TMDS_EQ1: U701.2 (EQ1)
TMDS_TX0N: J701.9 (D0-), U701.14 (OUT_D2N), U703.4 (IN3), U703.7 (OUT3)
TMDS_TX0P: J701.7 (D0+), U701.13 (OUT_D2P), U703.5 (IN4), U703.6 (OUT4)
TMDS_TX1N: J701.6 (D1-), U701.12 (OUT_D3N), U702.1 (IN1), U702.10 (OUT1)
TMDS_TX1P: J701.4 (D1+), U701.11 (OUT_D3P), U702.2 (IN2), U702.9 (OUT2)
TMDS_TX2N: J701.3 (D2-), U701.10 (OUT_D4N), U702.4 (IN3), U702.7 (OUT3)
TMDS_TX2P: J701.1 (D2+), U701.9 (OUT_D4P), U702.5 (IN4), U702.6 (OUT4)

Notes on the sheet:
EQ1 | EQ0 |SETTING ---------------- GND | GND | 0 dB GND | VDD | 2 dB VDD | GND | 4 dB VDD | VDD | 6 dB
On the hdmi connector void the plane underneat the TXP and TXN pins to reduce capacitance. Ref : Layout Guideline for PTN3366
MOUSE FPGA SERDES, RGB, & HDMI
LVDS TO TMDS
HDMI
LINE PROTECTION
RGB & LVDS OUTPUTS
