dennowiggle/FLEADiP/kicad/Mouse-vga.kicad_sch

## KiCad design kicad/Mouse-vga.kicad_sch (2023-07-13)

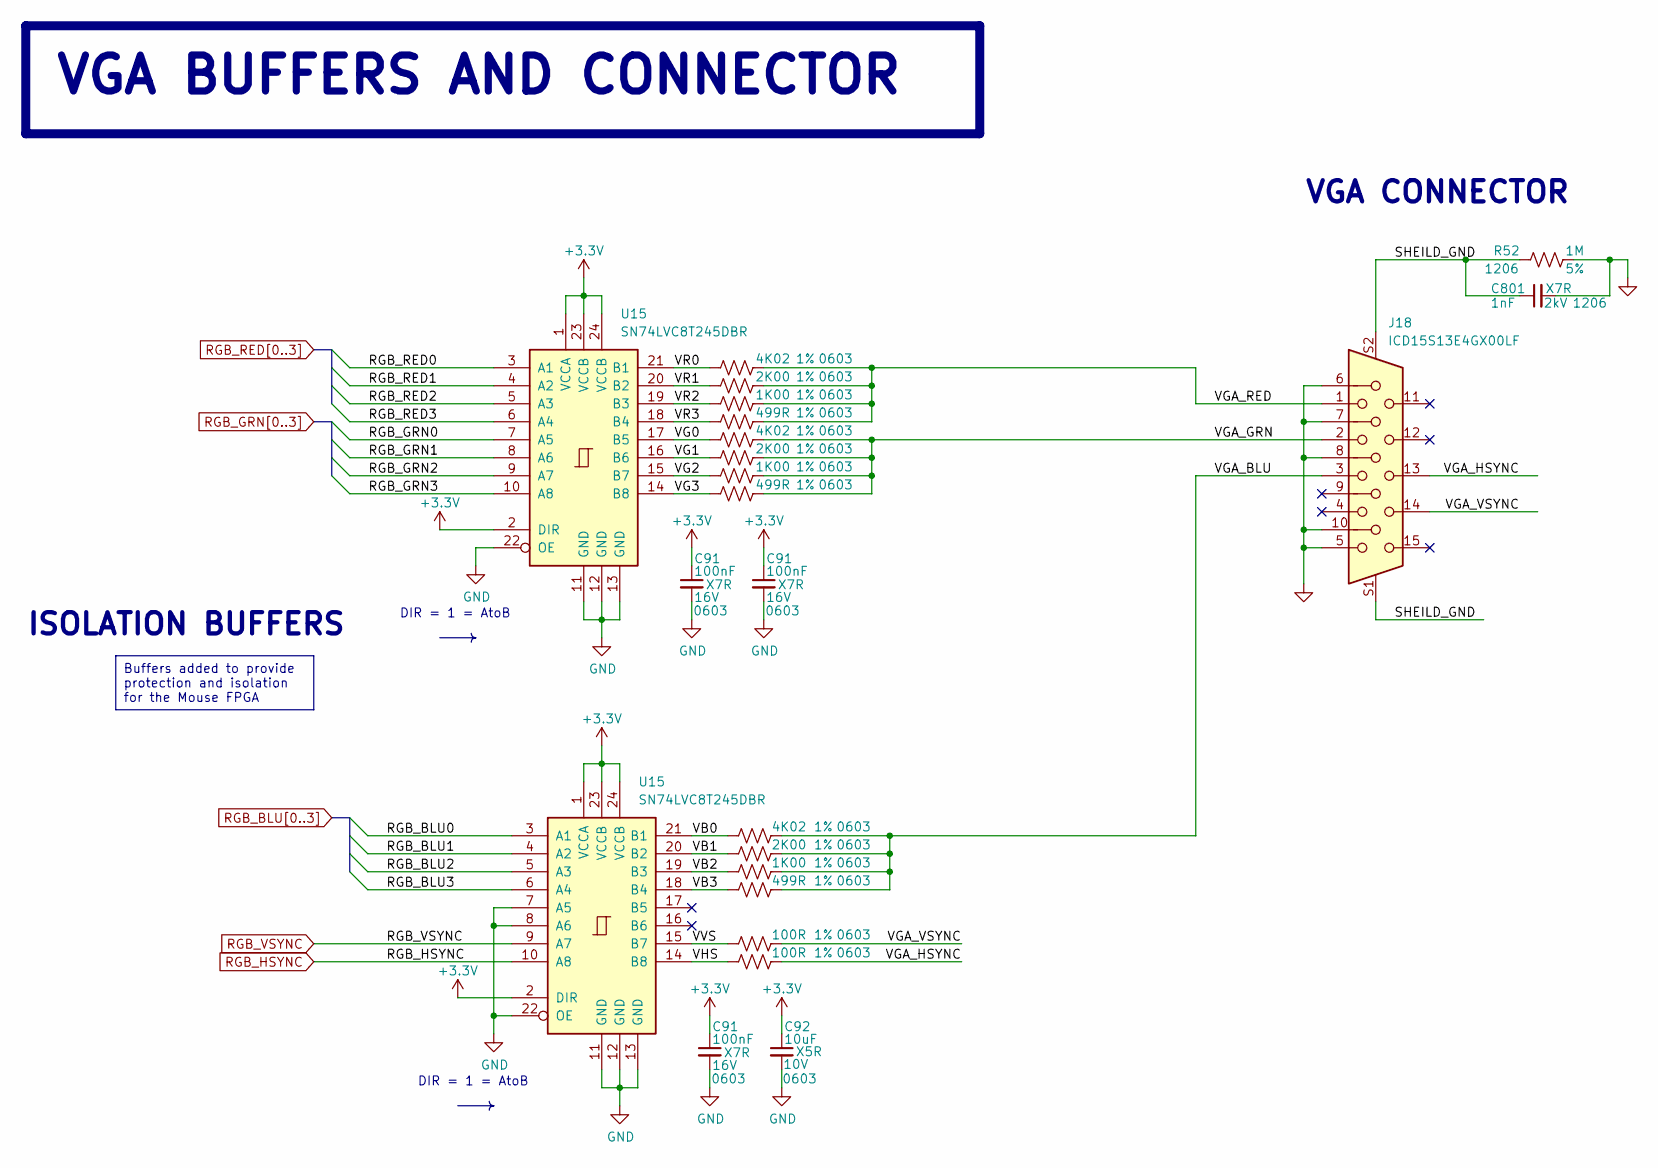
[picture p25: schematic Mouse-vga.kicad_sch]

Parts:
C91: 100nF; C_0603_1608Metric; Voltage 16V; Tolerance 10%; MPN CC0603KRX7R7BB104; Digikey 311-1088-1-ND
C92: 10uF; C_0603_1608Metric; Voltage 10V; Tolerance 10%; MPN CC0603KRX5R6BB106; Digikey 311-1782-1-ND
C801: 1nF; C_1206_3216Metric; Voltage 2kV; MPN VPDD202W102K1GV001E; Digikey 709-VPDD202W102K1GV001ECT-ND
J18: ICD15S13E4GX00LF; AMPHENOL_ICD15S13E4GX00LF; MPN ICD15S13E4GX00LF; Digikey 609-5181-ND
R52: 1M; R_1206_3216Metric; Tolerance 5%; MPN RC1206JR-071ML; Digikey 311-1.0MERCT-ND
R65: 100R; R_0603_1608Metric; Tolerance 1%; MPN RC0603FR-07100RL; Digikey 311-100HRCT-ND
U15: SN74LVC8T245DBR; SSOP-24_5.3x8.2mm_P0.65mm; MPN SN74LVC8T245DBR; Digikey 296-21065-1-ND

Connections:
+3.3V: C91.1, C92.1, U15.1 (VCCA), U15.2 (DIR), U15.23 (VCCB), U15.24 (VCCB)
GND: C91.2, C92.2, C801.2, J18.5, J18.6, J18.7, J18.8, J18.10, R52.2, U15.7 (A5), U15.8 (A6), U15.11 (GND), U15.12 (GND), U15.13 (GND), U15.22 (OE)
RGB_BLU0: U15.3 (A1)
RGB_BLU1: U15.4 (A2)
RGB_BLU2: U15.5 (A3)
RGB_BLU3: U15.6 (A4)
RGB_GRN0: U15.7 (A5)
RGB_GRN1: U15.8 (A6)
RGB_GRN2: U15.9 (A7)
RGB_GRN3: U15.10 (A8)
RGB_HSYNC: U15.10 (A8)
RGB_RED0: U15.3 (A1)
RGB_RED1: U15.4 (A2)
RGB_RED2: U15.5 (A3)
RGB_RED3: U15.6 (A4)
RGB_VSYNC: U15.9 (A7)
SHEILD_GND: C801.1, J18.S1 (SH1), J18.S2 (SH2), R52.1
VB0: R65.1, U15.21 (B1)
VB1: R65.1, U15.20 (B2)
VB2: R65.1, U15.19 (B3)
VB3: R65.1, U15.18 (B4)
VG0: R65.1, U15.17 (B5)
VG1: R65.1, U15.16 (B6)
VG2: R65.1, U15.15 (B7)
VG3: R65.1, U15.14 (B8)
VGA_BLU: J18.3, R65.2
VGA_GRN: J18.2, R65.2
VGA_HSYNC: J18.13, R65.2
VGA_RED: J18.1, R65.2
VGA_VSYNC: J18.14, R65.2
VHS: R65.1, U15.14 (B8)
VR0: R65.1, U15.21 (B1)
VR1: R65.1, U15.20 (B2)
VR2: R65.1, U15.19 (B3)
VR3: R65.1, U15.18 (B4)
VVS: R65.1, U15.15 (B7)

Notes on the sheet:
VGA BUFFERS AND CONNECTOR
Buffers added to provide protection and isolation for the Mouse FPGA
ISOLATION BUFFERS
DIR = 1 = AtoB
VGA CONNECTOR
