dennowiggle/FLEADiP/kicad/PowerSupply.kicad_sch

## KiCad design kicad/PowerSupply.kicad_sch (2023-07-13)

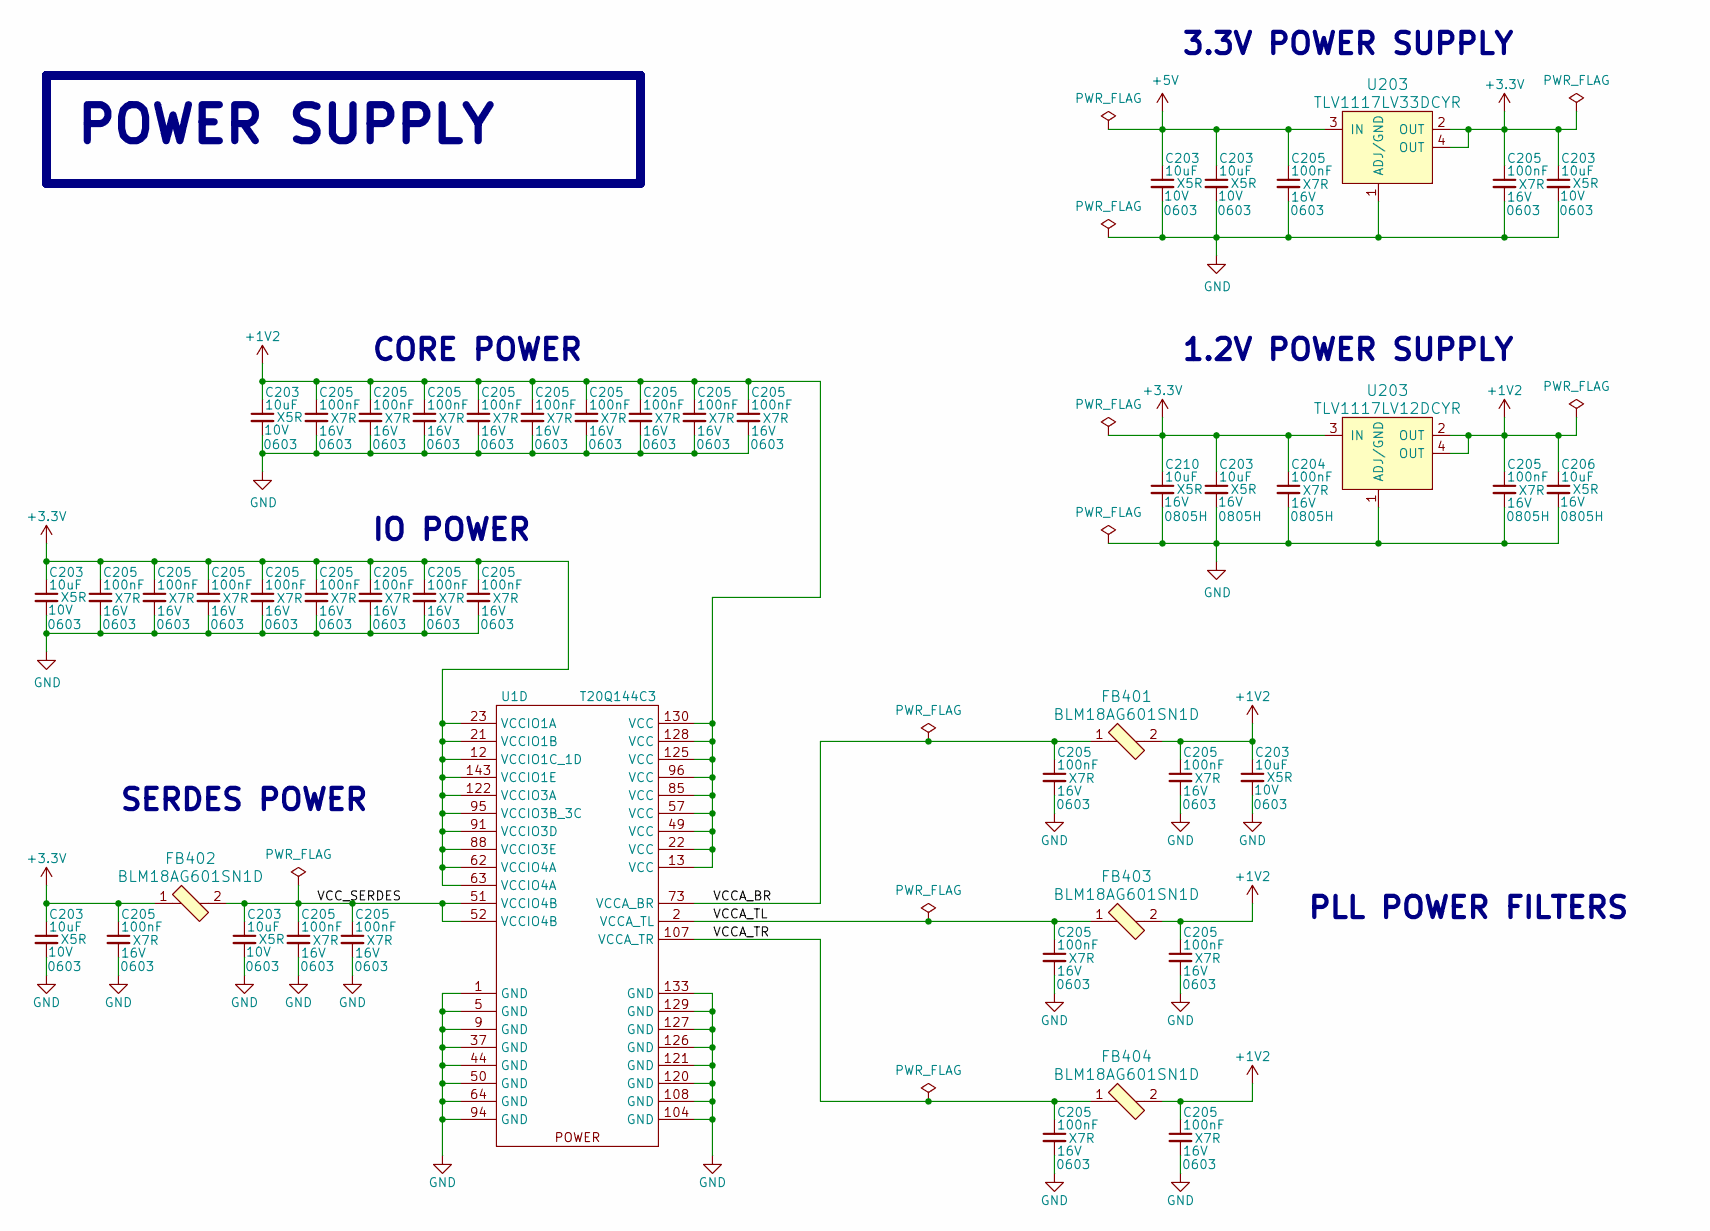
[picture p26: schematic PowerSupply.kicad_sch]

Parts:
C203: 10uF; C_0603_1608Metric; Voltage 10V; Tolerance 10%; MPN CC0603KRX5R6BB106; Digikey 311-1782-1-ND
C204, C205: 100nF; C_0805_2012Metric_Pad1.18x1.45mm_HandSolder; Voltage 16V; MPN 885012207045; Digikey 732-8045-1-ND
C206, C210: 10uF; C_0805_2012Metric_Pad1.18x1.45mm_HandSolder; Voltage 16V; MPN CL21A106KOQNNNG; Digikey 1276-6455-1-ND
FB401, FB402, FB403, FB404: BLM18AG601SN1D; L_0603_1608Metric; MPN BLM18AG601SN1D; Digikey 490-1014-1-ND
U1: T20Q144C3; LQFP-144_20x20mm_P0.5mm; MPN T20Q144C3; Digikey 2134-T20Q144C3-ND
U203: TLV1117LV12DCYR; SOT-223; MPN TLV1117LV12DCYR; Digikey 296-28776-1-ND

Connections:
+1V2: C203.1, C205.1, C206.1, FB401.2, FB403.2, FB404.2, U1.13 (VCC), U1.22 (VCC), U1.49 (VCC), U1.57 (VCC), U1.85 (VCC), U1.96 (VCC), U1.125 (VCC), U1.128 (VCC), U1.130 (VCC), U203.2 (OUT), U203.4 (OUT)
+3.3V: C203.1, C204.1, C205.1, C210.1, FB402.1, U1.12 (VCCIO1C_1D), U1.21 (VCCIO1B), U1.23 (VCCIO1A), U1.62 (VCCIO4A), U1.63 (VCCIO4A), U1.88 (VCCIO3E), U1.91 (VCCIO3D), U1.95 (VCCIO3B_3C), U1.122 (VCCIO3A), U1.143 (VCCIO1E), U203.2 (OUT), U203.3 (IN), U203.4 (OUT)
+5V: C203.1, C205.1, U203.3 (IN)
GND: C203.2, C204.2, C205.2, C206.2, C210.2, U1.1 (GND), U1.5 (GND), U1.9 (GND), U1.37 (GND), U1.44 (GND), U1.50 (GND), U1.64 (GND), U1.94 (GND), U1.104 (GND), U1.108 (GND), U1.120 (GND), U1.121 (GND), U1.126 (GND), U1.127 (GND), U1.129 (GND), U1.133 (GND), U203.1 (ADJ/GND)
VCCA_BR: C205.1, FB401.1, U1.73 (VCCA_BR)
VCCA_TL: C205.1, FB403.1, U1.2 (VCCA_TL)
VCCA_TR: C205.1, FB404.1, U1.107 (VCCA_TR)
VCC_SERDES: C203.1, C205.1, FB402.2, U1.51 (VCCIO4B), U1.52 (VCCIO4B)

Notes on the sheet:
POWER SUPPLY
1.2V POWER SUPPLY
SERDES POWER
IO POWER
3.3V POWER SUPPLY
CORE POWER
PLL POWER FILTERS
