dennowiggle/FLEADiP/kicad/Z80Interface.kicad_sch

## KiCad design kicad/Z80Interface.kicad_sch (2023-07-13)

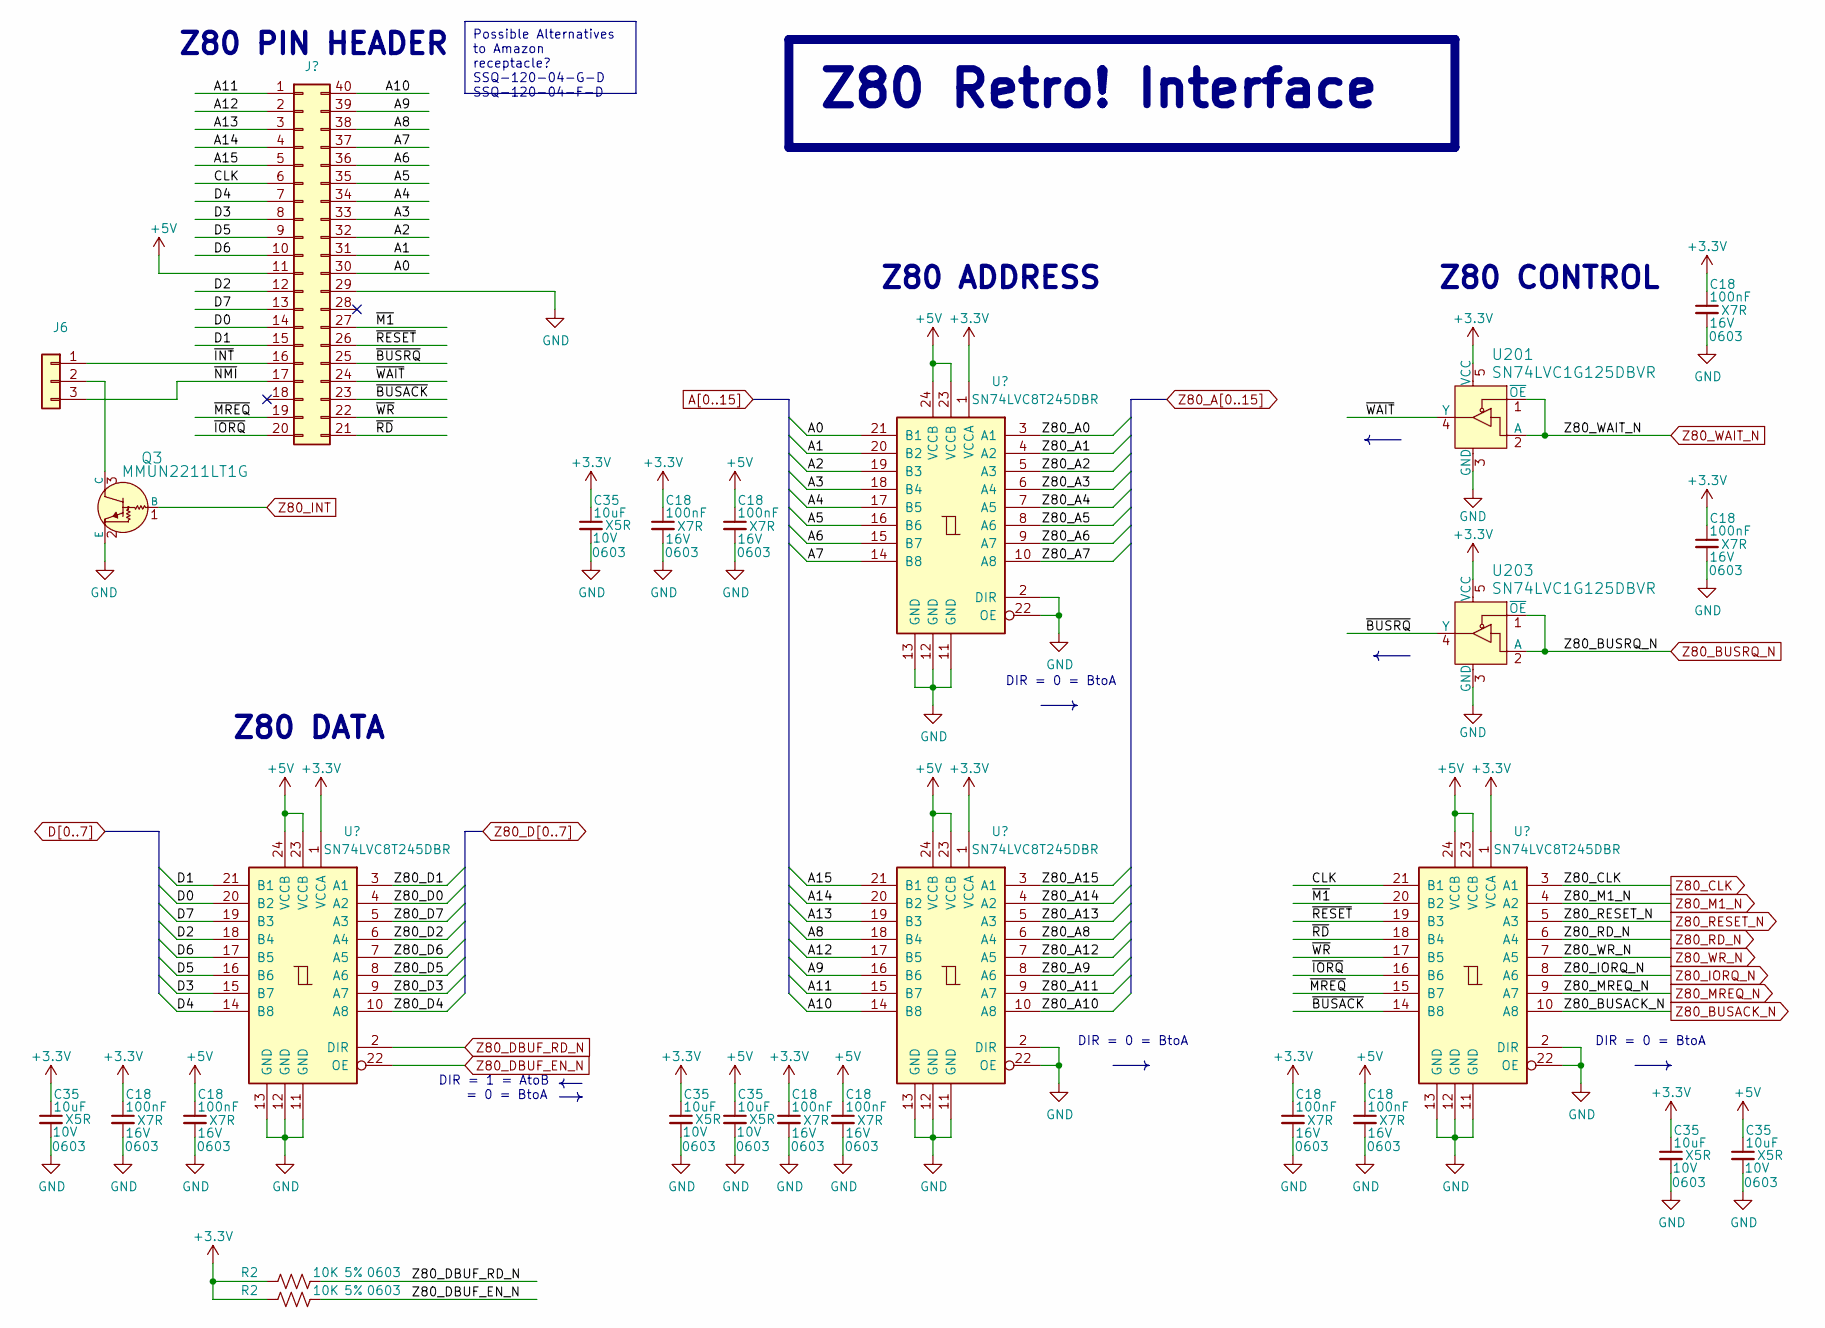
[picture p27: schematic Z80Interface.kicad_sch]

Parts:
C18: 100nF; C_0603_1608Metric; Voltage 16V; Tolerance 10%; MPN CC0603KRX7R7BB104; Digikey 311-1088-1-ND
C35: 10uF; C_0603_1608Metric; Voltage 10V; Tolerance 10%; MPN CC0603KRX5R6BB106; Digikey 311-1782-1-ND
J2: Conn_02x20_Counter_Clockwise; PinSocket_2x20_P2.54mm_Vertical_clockwise
J6: Conn_01x03; PinHeader_1x03_P2.54mm_Vertical; MPN PH1-03-UA; Digikey 2057-PH1-03-UA-ND
Q3: MMUN2211LT1G; SOT-23-3; MPN MMUN2211LT1G; Digikey MMUN2211LT1GOSCT-ND
R2: 10K; R_0603_1608Metric; Tolerance 5%; MPN RC0603JR-0710KL; Digikey 311-10KGRCT-ND
U201, U203: SN74LVC1G125DBVR; SOT-23-5_HandSoldering; MPN SN74LVC1G125DBVR; Digi-Key_PN 296-11603-1-ND
U202, U204, U205, U206: SN74LVC8T245DBR; SSOP-24_5.3x8.2mm_P0.65mm; MPN SN74LVC8T245DBR; Digikey 296-21065-1-ND

Connections:
+3.3V: C18.1, C35.1, R2.1, U201.5 (VCC), U202.1 (VCCA), U203.5 (VCC), U204.1 (VCCA), U205.1 (VCCA), U206.1 (VCCA)
+5V: C18.1, C35.1, J2.11, U202.23 (VCCB), U202.24 (VCCB), U204.23 (VCCB), U204.24 (VCCB), U205.23 (VCCB), U205.24 (VCCB), U206.23 (VCCB), U206.24 (VCCB)
A0: J2.30, U202.21 (B1)
A1: J2.31, U202.20 (B2)
A2: J2.32, U202.19 (B3)
A3: J2.33, U202.18 (B4)
A4: J2.34, U202.17 (B5)
A5: J2.35, U202.16 (B6)
A6: J2.36, U202.15 (B7)
A7: J2.37, U202.14 (B8)
A8: J2.38, U205.18 (B4)
A9: J2.39, U205.16 (B6)
A10: J2.40, U205.14 (B8)
A11: J2.1, U205.15 (B7)
A12: J2.2, U205.17 (B5)
A13: J2.3, U205.19 (B3)
A14: J2.4, U205.20 (B2)
A15: J2.5, U205.21 (B1)
CLK: J2.6, U206.21 (B1)
D0: J2.14, U204.20 (B2)
D1: J2.15, U204.21 (B1)
D2: J2.12, U204.18 (B4)
D3: J2.8, U204.15 (B7)
D4: J2.7, U204.14 (B8)
D5: J2.9, U204.16 (B6)
D6: J2.10, U204.17 (B5)
D7: J2.13, U204.19 (B3)
GND: C18.2, C35.2, J2.29, Q3.2 (E), U201.3 (GND), U202.2 (DIR), U202.11 (GND), U202.12 (GND), U202.13 (GND), U202.22 (OE), U203.3 (GND), U204.11 (GND), U204.12 (GND), U204.13 (GND), U205.2 (DIR), U205.11 (GND), U205.12 (GND), U205.13 (GND), U205.22 (OE), U206.2 (DIR), U206.11 (GND), U206.12 (GND), U206.13 (GND), U206.22 (OE)
unnamed: J6.2, Q3.3 (C)
Z80_A0: U202.3 (A1)
Z80_A1: U202.4 (A2)
Z80_A2: U202.5 (A3)
Z80_A3: U202.6 (A4)
Z80_A4: U202.7 (A5)
Z80_A5: U202.8 (A6)
Z80_A6: U202.9 (A7)
Z80_A7: U202.10 (A8)
Z80_A8: U205.6 (A4)
Z80_A9: U205.8 (A6)
Z80_A10: U205.10 (A8)
Z80_A11: U205.9 (A7)
Z80_A12: U205.7 (A5)
Z80_A13: U205.5 (A3)
Z80_A14: U205.4 (A2)
Z80_A15: U205.3 (A1)
Z80_BUSACK_N: U206.10 (A8)
Z80_BUSRQ_N: U203.1 (~OE), U203.2 (A)
Z80_CLK: U206.3 (A1)
Z80_D0: U204.4 (A2)
Z80_D1: U204.3 (A1)
Z80_D2: U204.6 (A4)
Z80_D3: U204.9 (A7)
Z80_D4: U204.10 (A8)
Z80_D5: U204.8 (A6)
Z80_D6: U204.7 (A5)
Z80_D7: U204.5 (A3)
Z80_DBUF_EN_N: R2.2, U204.22 (OE)
Z80_DBUF_RD_N: R2.2, U204.2 (DIR)
Z80_INT: Q3.1 (B)
Z80_IORQ_N: U206.8 (A6)
Z80_M1_N: U206.4 (A2)
Z80_MREQ_N: U206.9 (A7)
Z80_RD_N: U206.6 (A4)
Z80_RESET_N: U206.5 (A3)
Z80_WAIT_N: U201.1 (~OE), U201.2 (A)
Z80_WR_N: U206.7 (A5)
~BUSACK: J2.23, U206.14 (B8)
~BUSRQ: J2.25, U203.4 (Y)
~INT: J2.16, J6.1
~IORQ: J2.20, U206.16 (B6)
~M1: J2.27, U206.20 (B2)
~MREQ: J2.19, U206.15 (B7)
~NMI: J2.17, J6.3
~RD: J2.21, U206.18 (B4)
~RESET: J2.26, U206.19 (B3)
~WAIT: J2.24, U201.4 (Y)
~WR: J2.22, U206.17 (B5)

Notes on the sheet:
Z80 Retro! Interface
Possible Alternatives to Amazon receptacle? SSQ-120-04-G-D SSQ-120-04-F-D
Z80 PIN HEADER
DIR = 0 = BtoA
Z80 CONTROL
Z80 DATA
DIR = 1 = AtoB = 0 = BtoA
Z80 ADDRESS
